TinyCircuits/TinyCircuits-TinyDuino-ASM2001/images/ASM2001-R-L-Tutorial-Image-01.png

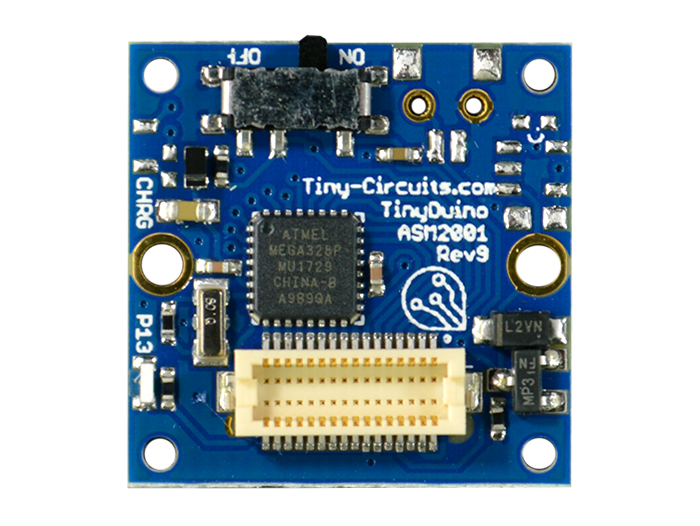
images/ASM2001-R-L-Tutorial-Image-01.png
