TinyCircuits/TinyCircuits-TinyDuino-ASM2001/images/ASM2001-R-L-Tutorial-Image-02.jpg

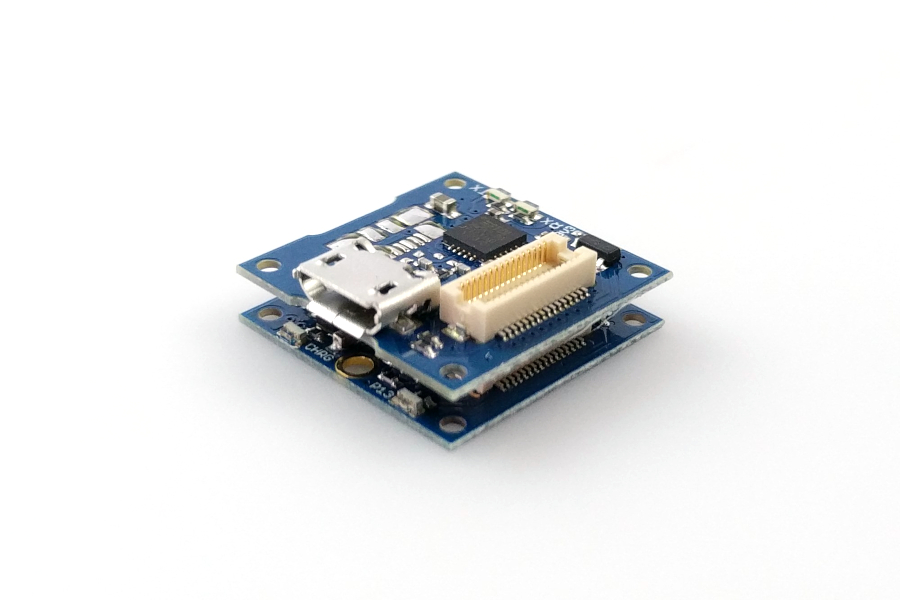
images/ASM2001-R-L-Tutorial-Image-02.jpg
