TinyCircuits/TinyCircuits-TinyDuino-ASM2001/images/tutorial_images/ASM2001-Tutorial-Image-02.jpg

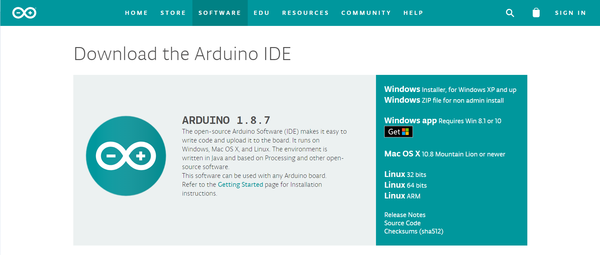
images/tutorial_images/ASM2001-Tutorial-Image-02.jpg
