TinyCircuits/TinyCircuits-TinyDuino-ASM2001/images/tutorial_images/ASM2001-Tutorial-Image-07.jpg

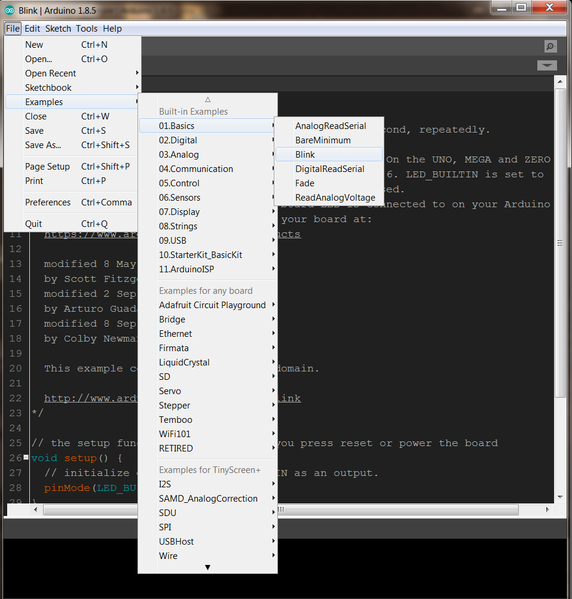
images/tutorial_images/ASM2001-Tutorial-Image-07.jpg
