TinyCircuits/TinyCircuits-TinyDuino-ASM2001/images/tutorial_images/ASM2001-Tutorial-Image-08.jpg

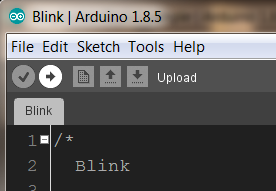
images/tutorial_images/ASM2001-Tutorial-Image-08.jpg
